FarmBoy522/CapstonePDr.Brown/MichaelKisellus-Folder/Sprint_v2_Kisellus.pptx

## Portable Ultrasound Device for Coda-Wave Interferometry Sprint 2

Prepared by Michael Kisellus, Christopher Coppedge, Leyton Foxworthy, Matthew Baker, Kyle Fox
27OCT2023

## What is this projects goal?

- Produce a handheld ultrasound inspection device for inspecting a bridge/structural component for faults in the field.
- This handheld unit gathers and stores test data collected over time 72 hours.
- Budget - $2000
Existing commercial solution:
- Expensive ($5200)
- Is not able to record without an operator present

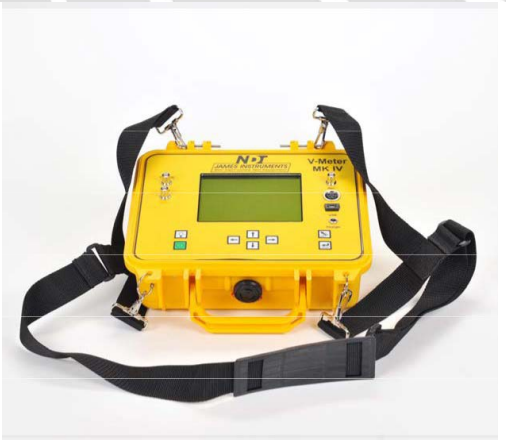
[picture p25: figure]

## Background:

- Civil engineering lab has a concrete “scanning” process that involves measuring how ultrasonic waves travel through the concrete

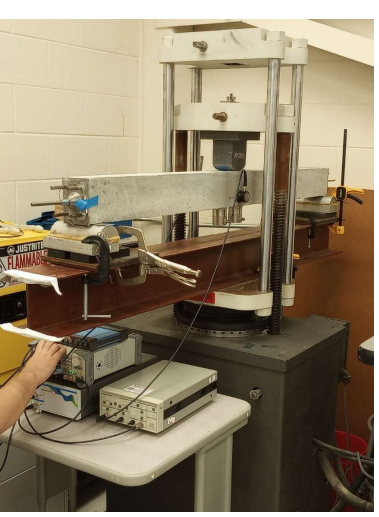
[picture p26: figure]
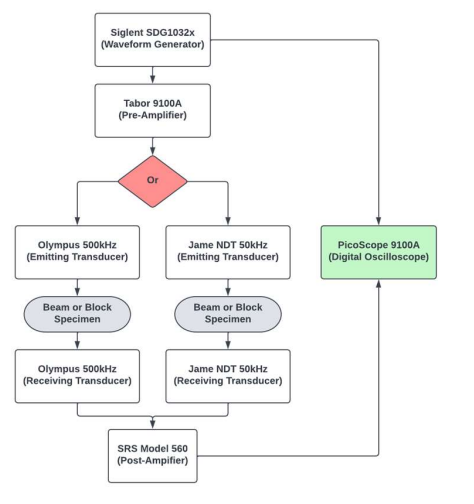
[picture p27: figure]

## Background:

- Data analysis (through MATLAB) is able to reveal imperfections in the concrete.

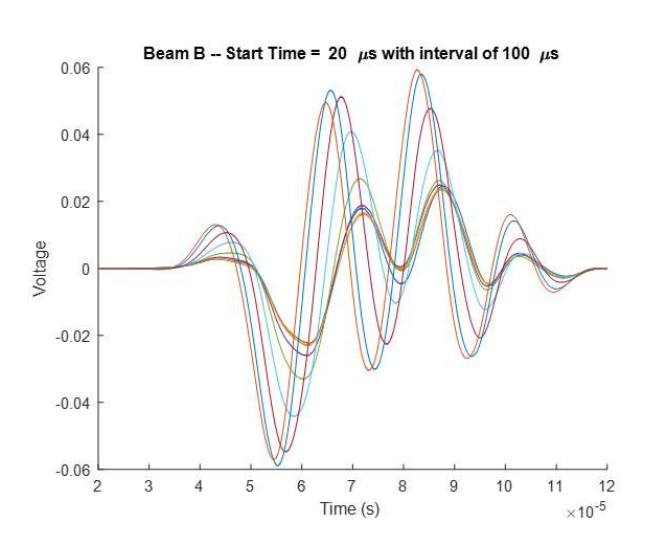
[picture p28: figure]

Scan of a compromised piece of concrete

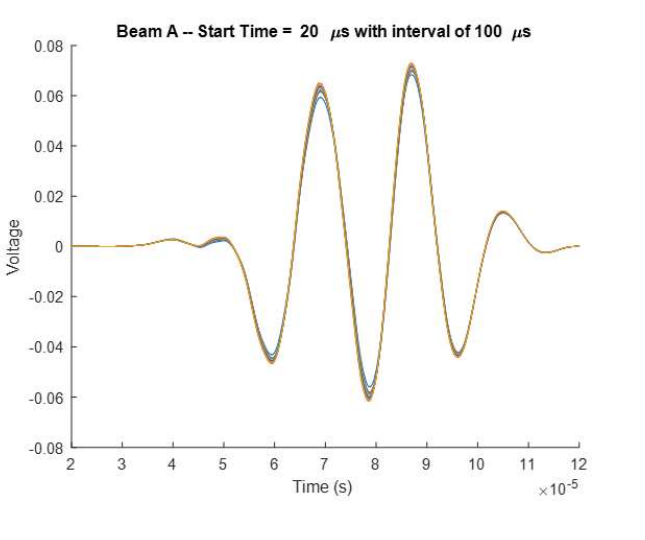
[picture p29: figure]

Scan of a proper piece of concrete

## Overview of previous sprint (background)

- Coordinating with client to understand scope of project
- Division of responsibilities
- Preliminary design
- Establish budget and parts list
- Research parts/ data sheets
- SRS, SDS, Test Plan

## Progress compared to previous sprint (Work completed)

- Electrical system design completed.
Changed: MOSFETS, and added a discharge loop for capacitor.
- Cooling system
- Software
- Tx and Rx system
- Control system
- Enclosure system

## Slide 7

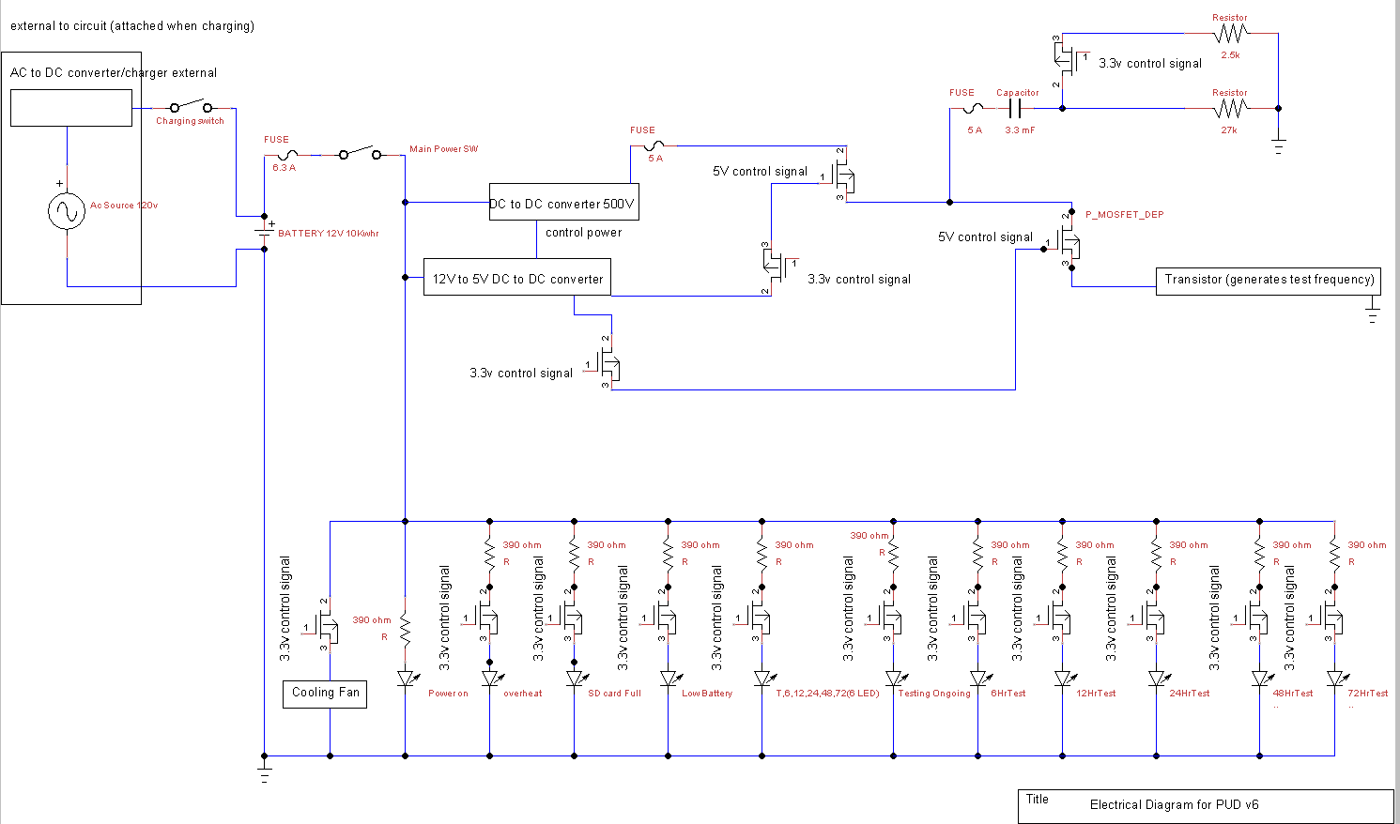
[picture p30: figure]

## Current Status

- Electrical system design complete and waiting for parts.
- Cooling system
- Software
- Tx and Rx system
- Control system
- Enclosure system

## Roles of the Team Members

- Michael Kisellus: Electrical system, SDD,SRS
- Christopher Coppedge: Enclosure system, parts and acquisition
- Leyton Foxworthy: Software
- Matthew Baker: Cooling system
- Kyle Fox: Tx and Rx system, Control system

## Preview of next sprint goals (Work remaining)

- Order/ receive parts
- Test components individually
- Assemble parts into designed system
- Program control systems
- Test systems per test plan
- Troubleshoot as required

## Risks or Issues

- Part delay of 30 days for 12v to 500v DC to DC converter
- High voltage 500V DC present in system. Client requests instructor permission prior to working on the 500 v section.

## Visual Demo (video recording, live demo, etc.)

- N/A

## Questions?

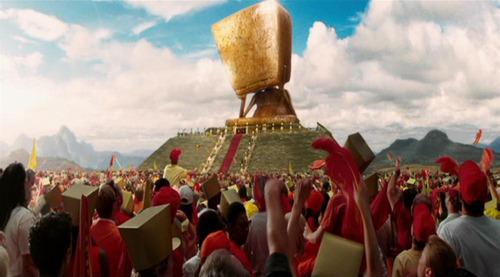
[picture p31: figure]
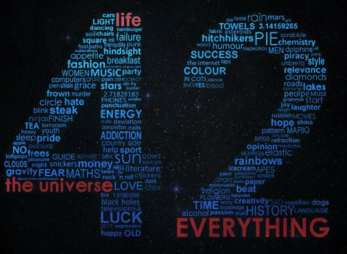
[picture p32: figure]
