FarmBoy522/CapstonePDr.Brown/MichaelKisellus-Folder/Sprint1_Presentation_draft_kisellus.pptx

## Portable Ultrasound Device for Coda-Wave Interferometry Sprint 1

Prepared by Michael Kisellus, Christopher Coppedge, Leyton Foxworthy, Matthew Baker, Kyle Fox
02OCT2023

## What is this projects goal?

- Produce a handheld ultrasound inspection device for inspecting a bridge/structural component for faults in the field.
- This handheld unit gathers and stores test data collected over time 72 hours.

## Overall system diagram

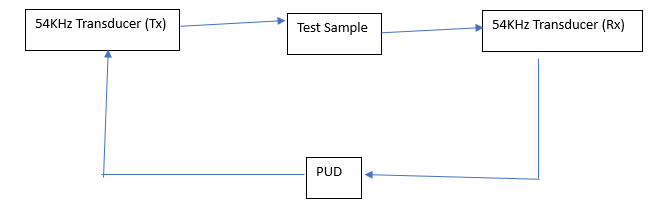
[picture p33: figure]

## Portable Ultrasound Device (PUD) diagram

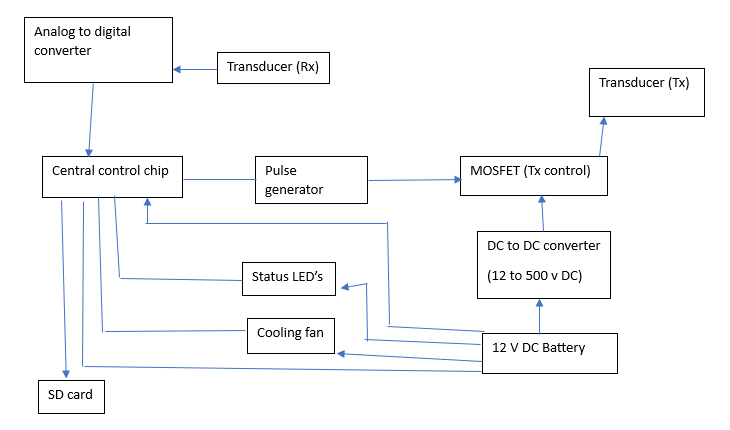
[picture p34: figure]

## Operation panel layout

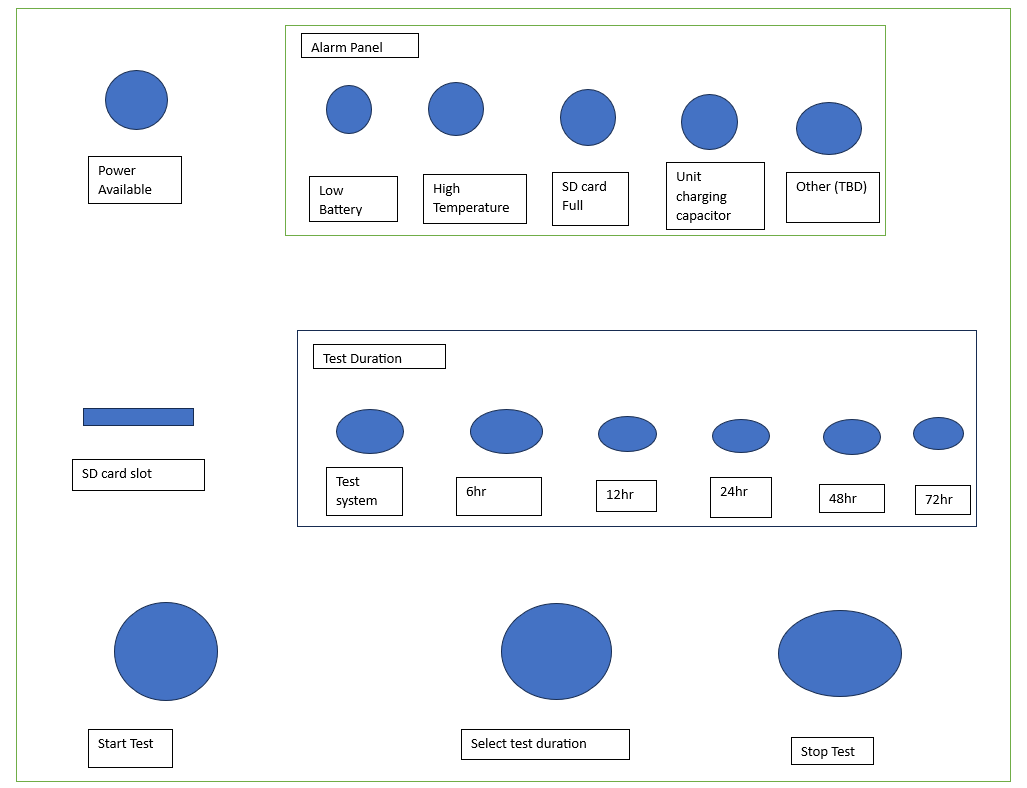
[picture p35: figure]

## Sub Systems

- Electrical system
- Cooling system
- Transmission(Tx) and Receiving(Rx) system
- Control system
- Enclosure system

## Electrical system 500V DC section

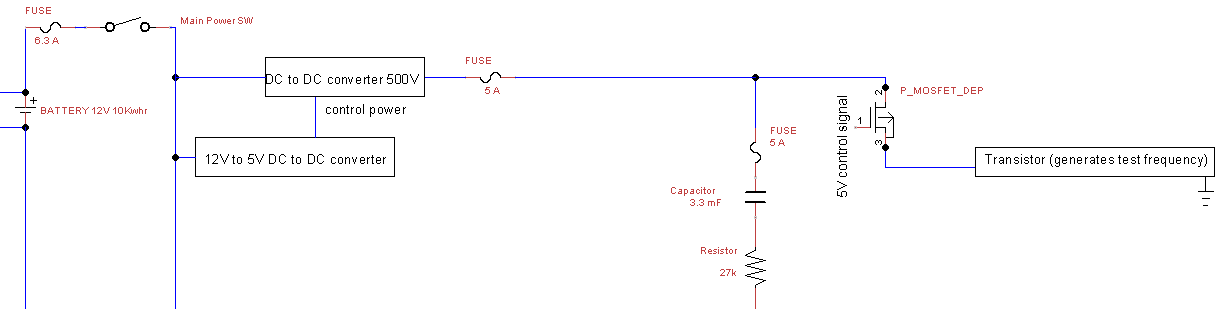
[picture p36: figure]

## Electrical system 12 V DC load section

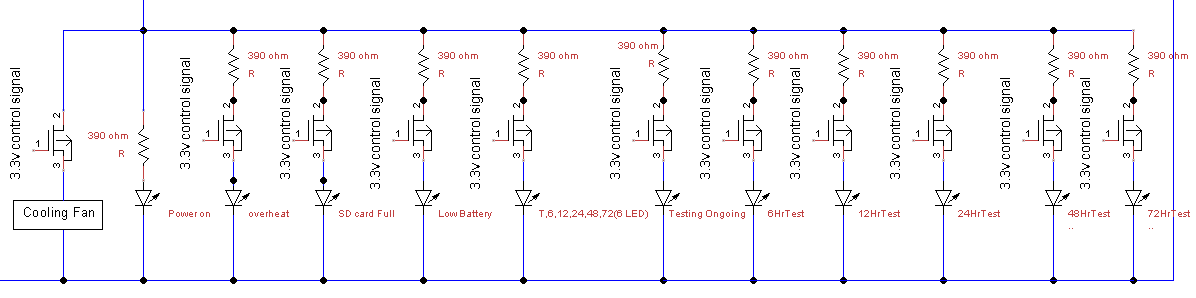
[picture p37: figure]

## Slide 9

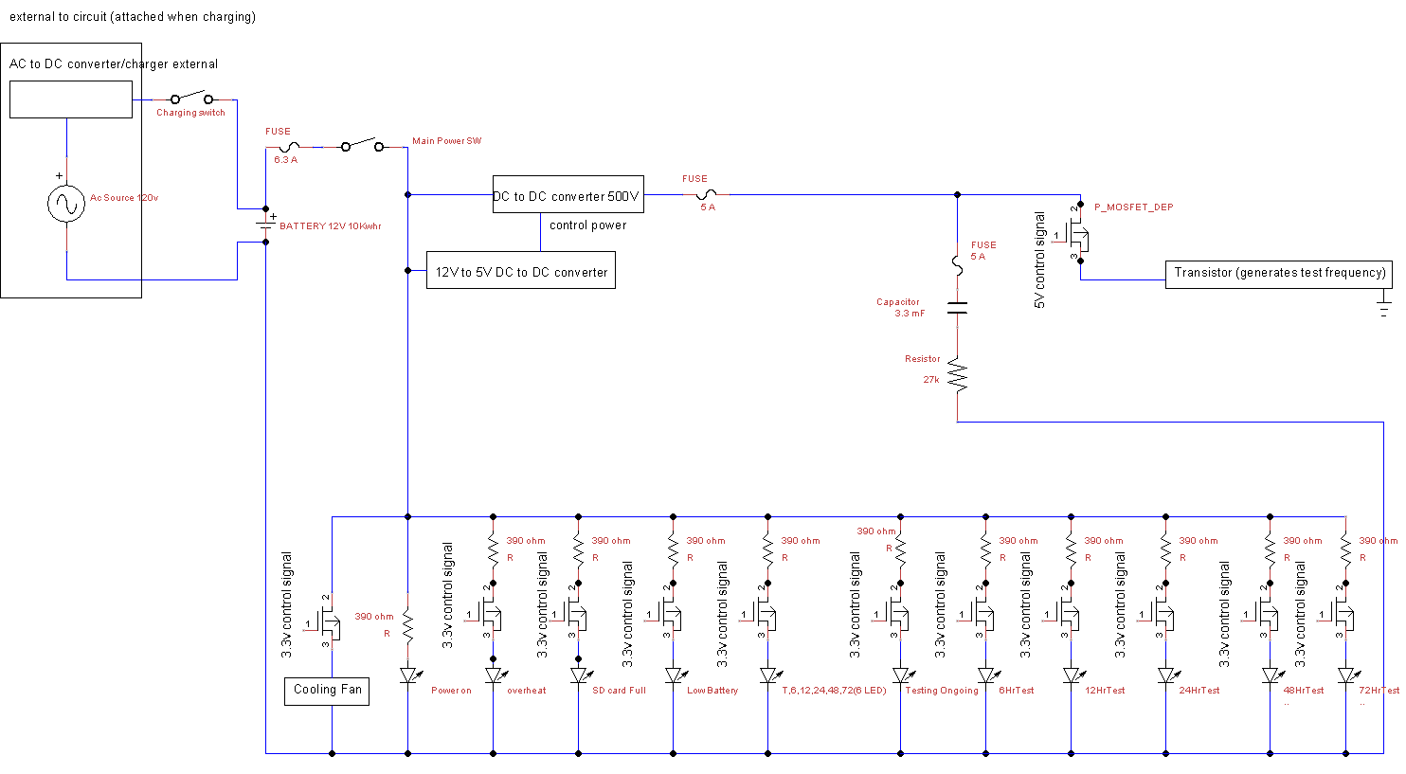
[picture p38: figure]

## Electrical system main requirements

- Operate for 48 to 72 hr without charging
- Produce 500V DC
- Produce 12 V DC

## Next subsystem
