FarmBoy522/CapstonePDr.Brown/Deliverables/Sprint 6/Backlog_Summary_Document.docx

PUD Project Brag Sheet

Michael Kisellus:

Major contribution summary: Constructing, mounting, testing, and repair/troubleshoot the electrical system.

Man hours: 72

(12 weeks) approximately 6hrs/ week (Averaged out more at start and less now)

Tasks completed: 40/43

Leyton Foxworthy

Major contribution summary: Software: adapted and altered existing picoscope ide to work in python and coded sample procedure for final product.

Man hours: 50

Tasks completed: 14/24 (needs to update progress/ not current)

Kyle Fox

Major contribution summary: Microcontroller Programming, Oscilloscope

Man hours: 50

Tasks completed: 8/18

Christopher Coppedge

Major contribution summary: Financial management, parts acquisition, documentation / proofreading.

Man hours: 45-55 (Average 4 -5 hours per week)

Tasks completed: 15/16

Matthew Baker

Major contribution summary: Cooling System parts researching, programming, installation, additional documentation/proofreading

Man hours: 36

Tasks completed: 12/12
