FarmBoy522/CapstonePDr.Brown/MichaelKisellus-Folder/Schematic_electrical_v17.docx

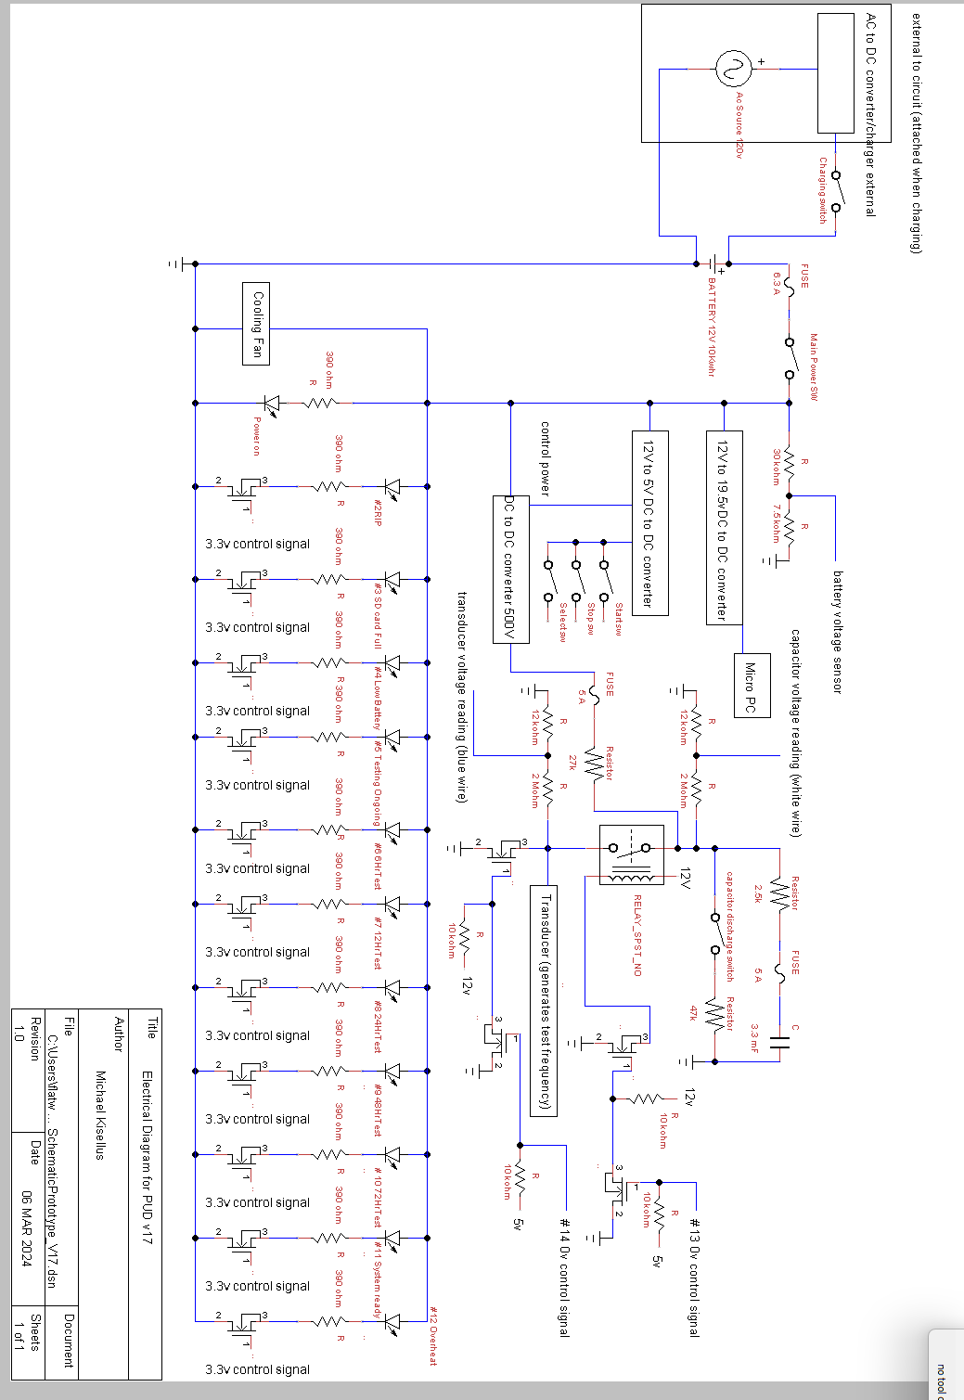
[picture p69: figure]
