FarmBoy522/CapstonePDr.Brown/MichaelKisellus-Folder/james institute transducer.docx

https://www.ndtjames.com/54_Khz_Ultrasonic_Transducer_p/v-c-4898.htm

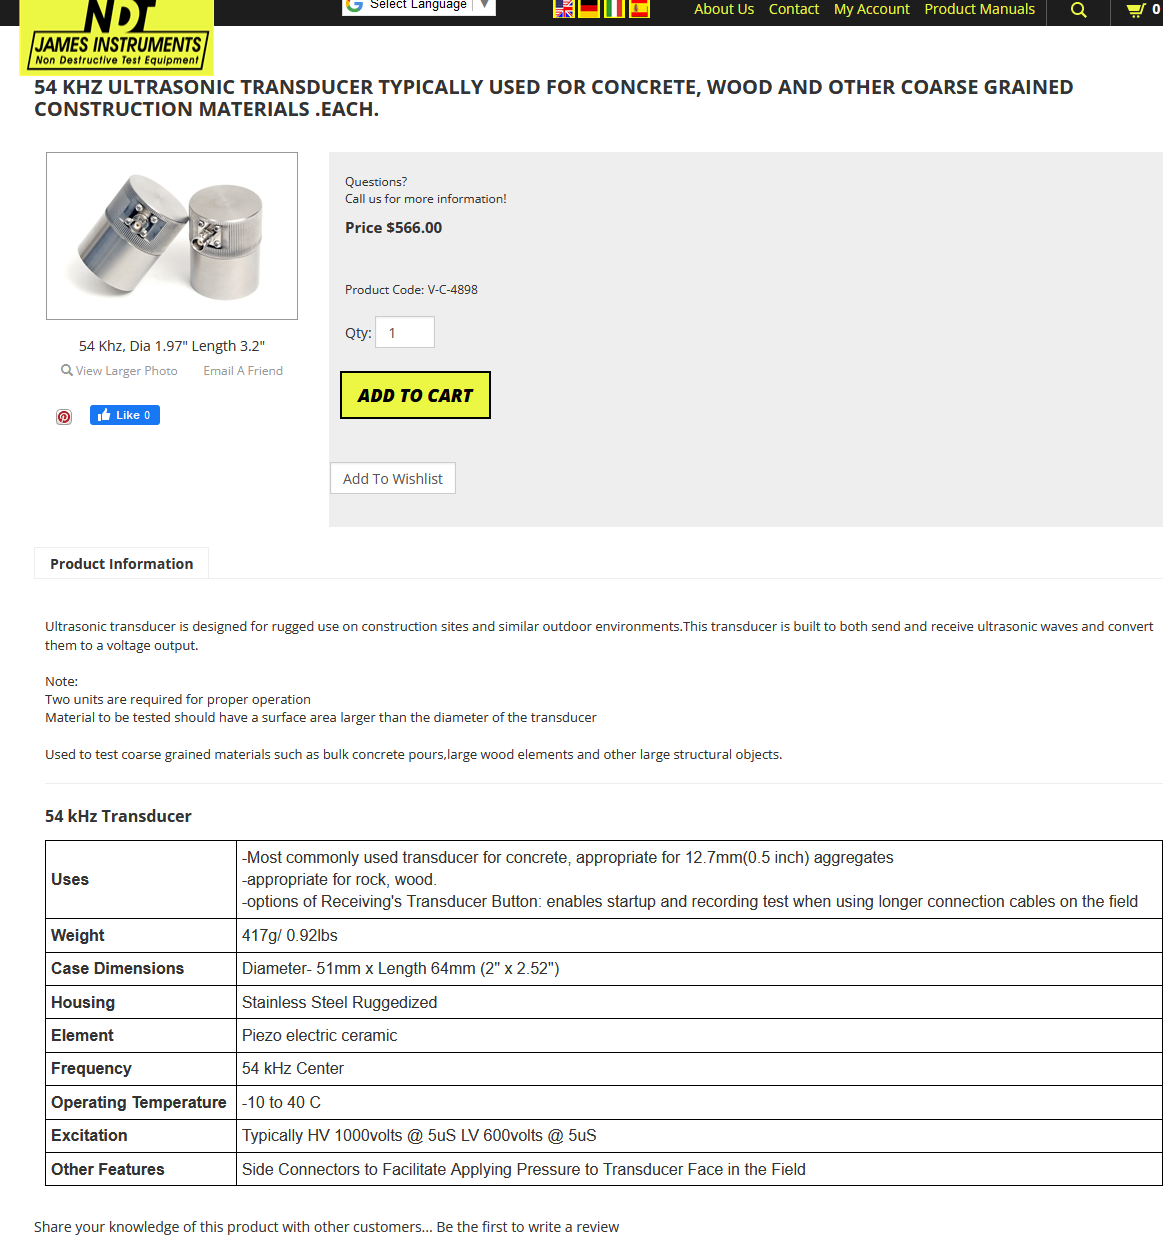
[picture p70: figure]

Excitation Typically HV 1000volts @ 5uS LV 600volts @ 5uS

https://www.ndtjames.com/Ultrasonic-Transducers_a/315.html

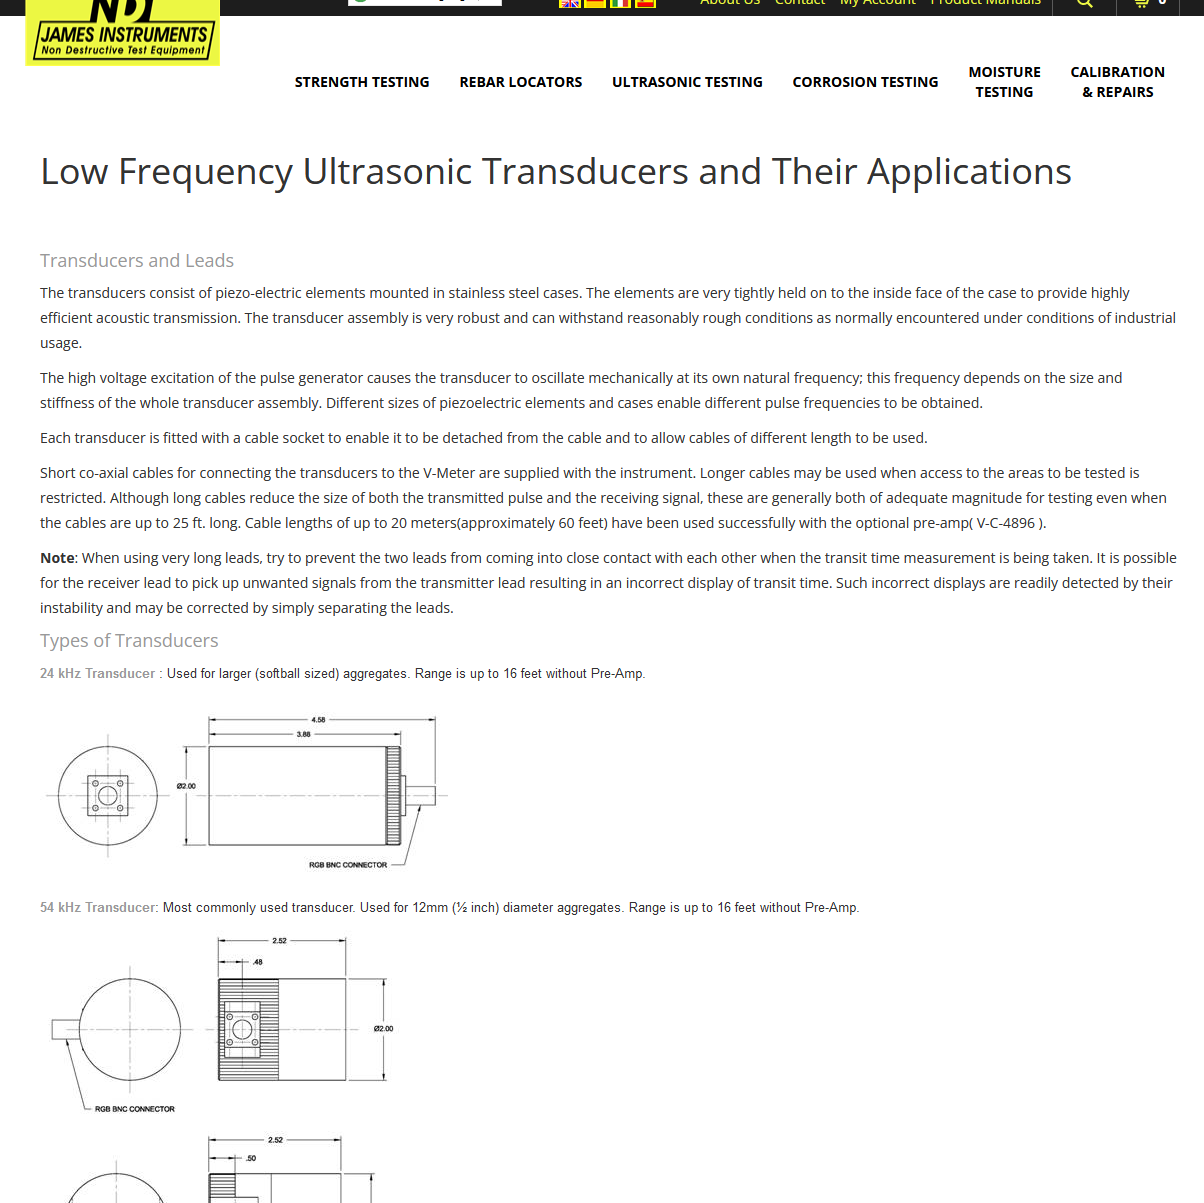
[picture p71: figure]
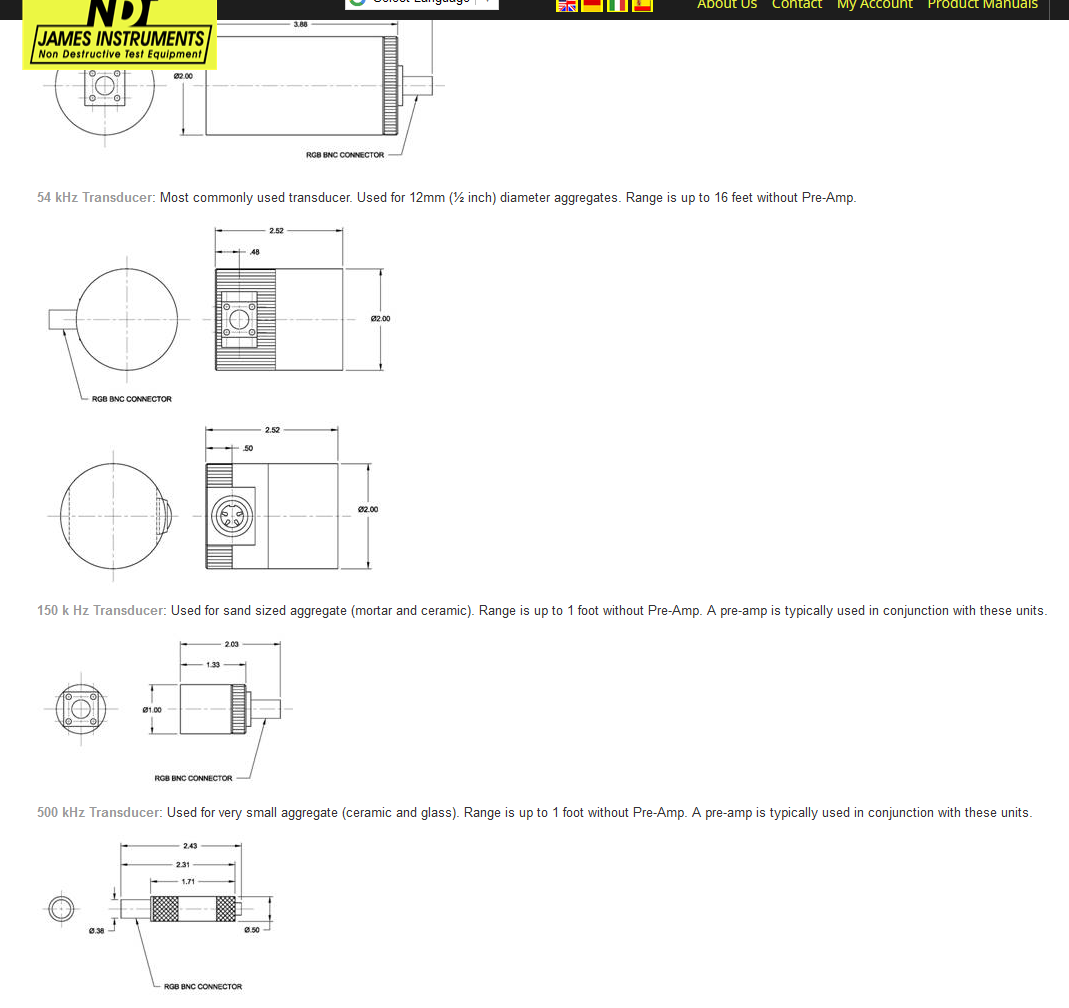
[picture p72: figure]

https://onestoptesting.co.uk/wp-content/uploads/2016/04/V-C-9900.pdf

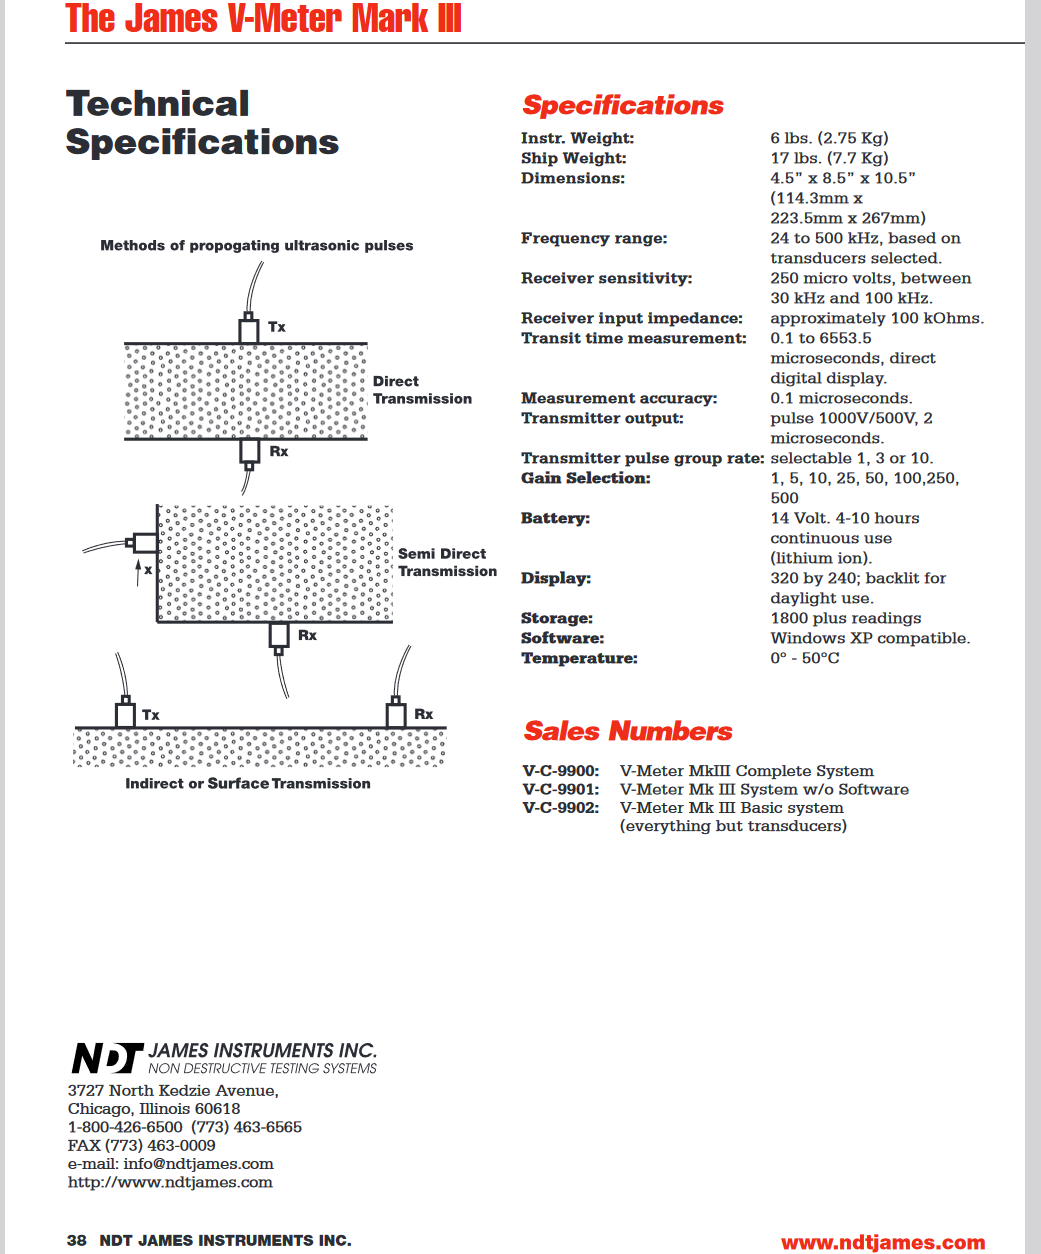
[picture p73: figure]

500kHz

https://www.ndtjames.com/500_Khz_Dia_6_0_Mm_p/v-c-7217.htm

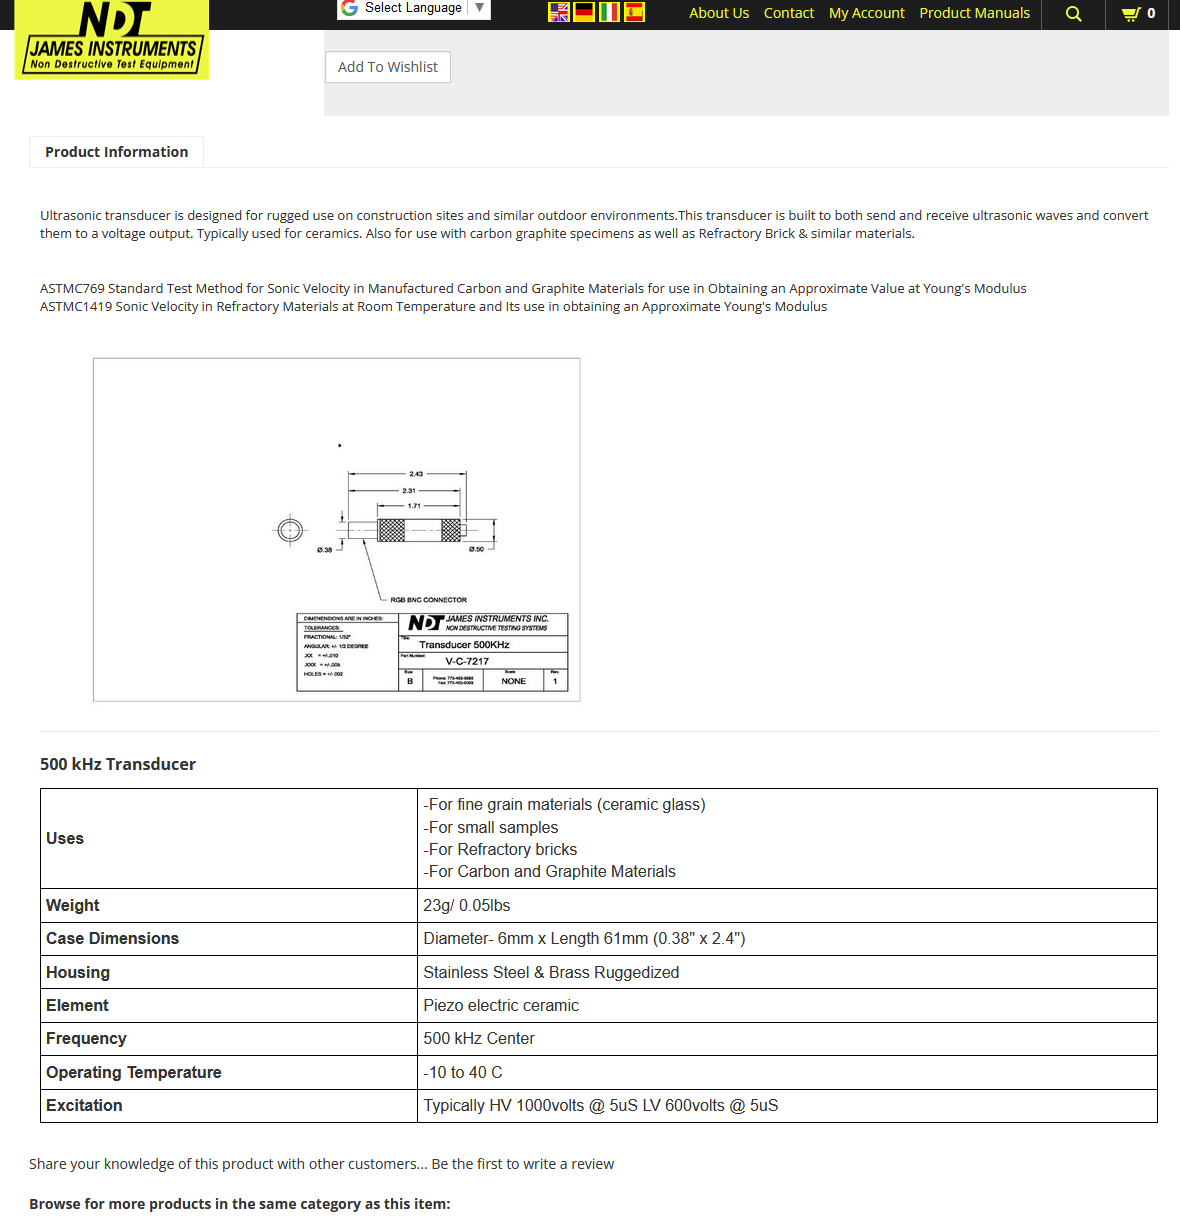
[picture p74: figure]
