FarmBoy522/CapstonePDr.Brown/MatthewBaker-Folder/Semester1/Cooling_Mockup_SheetMethod.pdf

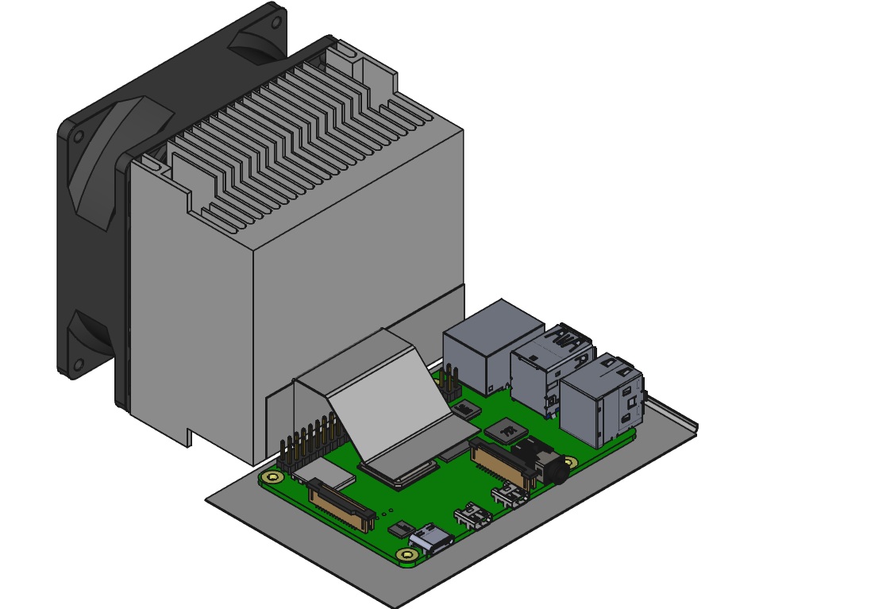
[picture p75: page 1]
